takusan213/usb-ss-gamepad/software/project_SS_gamepad.X/my_usb_pid.h

/*******************************************************************************
 * Copyright 2022 Geeky Fab. (geekyfab.com)
 * 
 * !!!!!CAUTION!!!!!
 * You CAN'T use this PID(0xE76C) for commercial use.
 * To use PID for commercial use, you have to take your own PID.
*******************************************************************************/

#ifndef MY_USB_PID_H
#define	MY_USB_PID_H

#define MY_USB_PID 0xE76C

#endif	/* MY_USB_PID_H */
